sgmk/BlinkeShit3000/Blinkeshit_Bitw/PCB/taefeli_Top_export.png

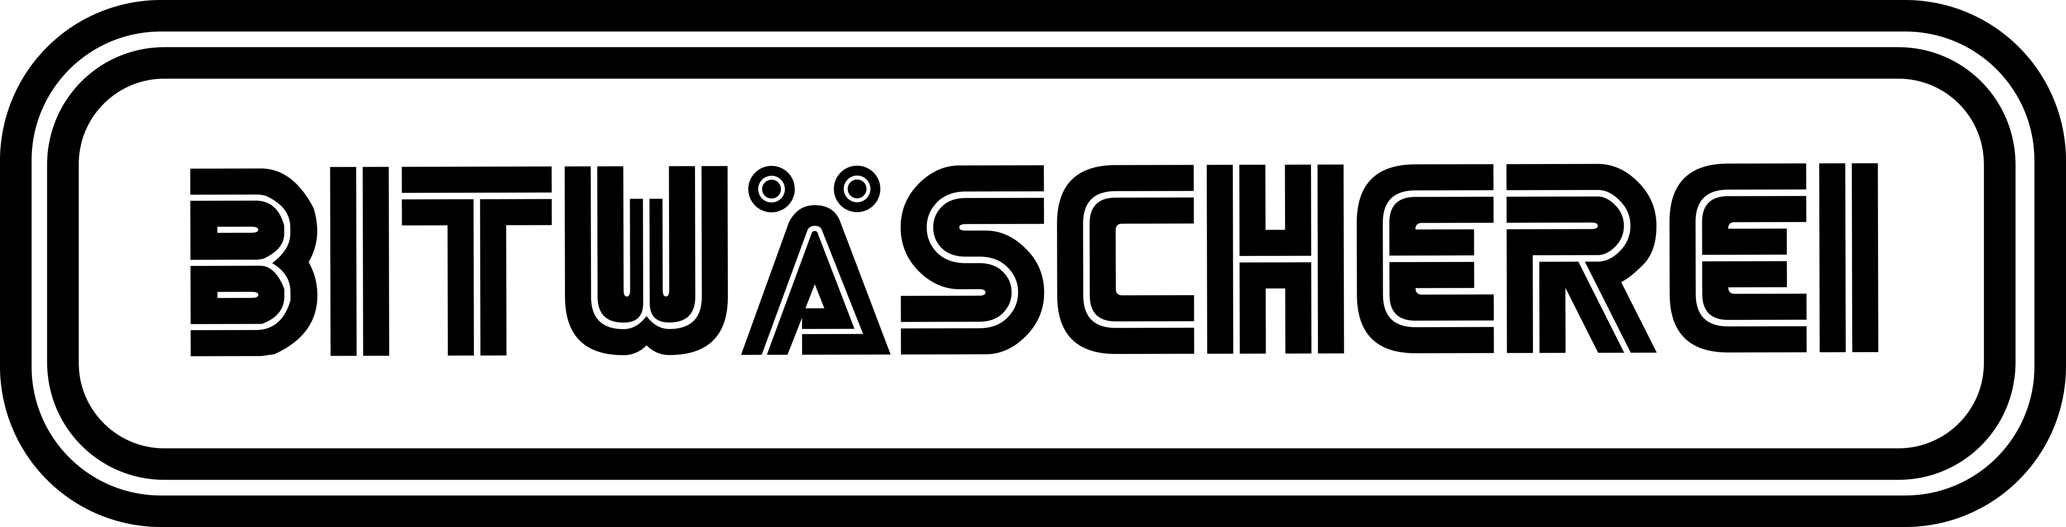
Blinkeshit_Bitw/PCB/taefeli_Top_export.png
