sgmk/BlinkeShit3000/LUMA-box-hacked/Werkspionage_Basel_2020_etching.jpg

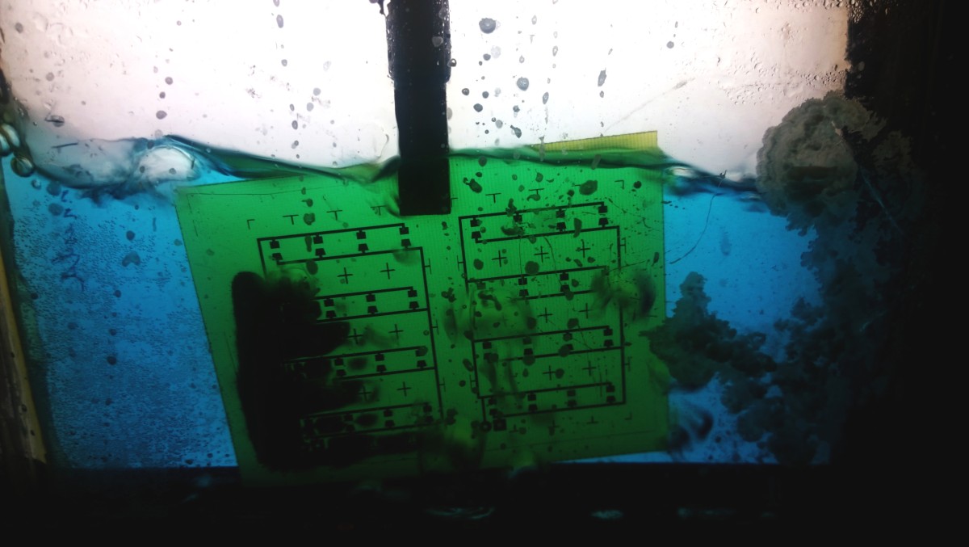
LUMA-box-hacked/Werkspionage_Basel_2020_etching.jpg
