sgmk/BlinkeShit3000/Blinkeshit_Bitw/3d_case/BlinkeShit_Case.scad

//14 9
WallThickness = 1.4;
StepThickness = 1.8;
Height = 8;
StepHeight = 1.4;
CoverHeight = 1.2;


   
 //linear_extrude(height = 2, center = false, convexity = 10, twist = 0) import("2s_Border_inner.dxf", convexity=3);
 
  linear_extrude(height = 20, center = false, convexity = 10, twist = 0) import("2d_wall.dxf", convexity=3);

 
  //linear_extrude(height = 1.2, center = false, convexity = 10, twist = 0) import("2d_cover.dxf", convexity=3); 
  
  //translate([0,0,0]) linear_extrude(height = 8.2, center = false, convexity = 10, twist = 0) import("2d_randli.dxf", convexity=3);
  
  translate([0,0,0]) linear_extrude(height = 1.2, center = false, convexity = 10, twist = 0) import("2d_top.dxf", convexity=3);
 
